KTH-RPL/Pluto-ATRV/images/gps.jpg

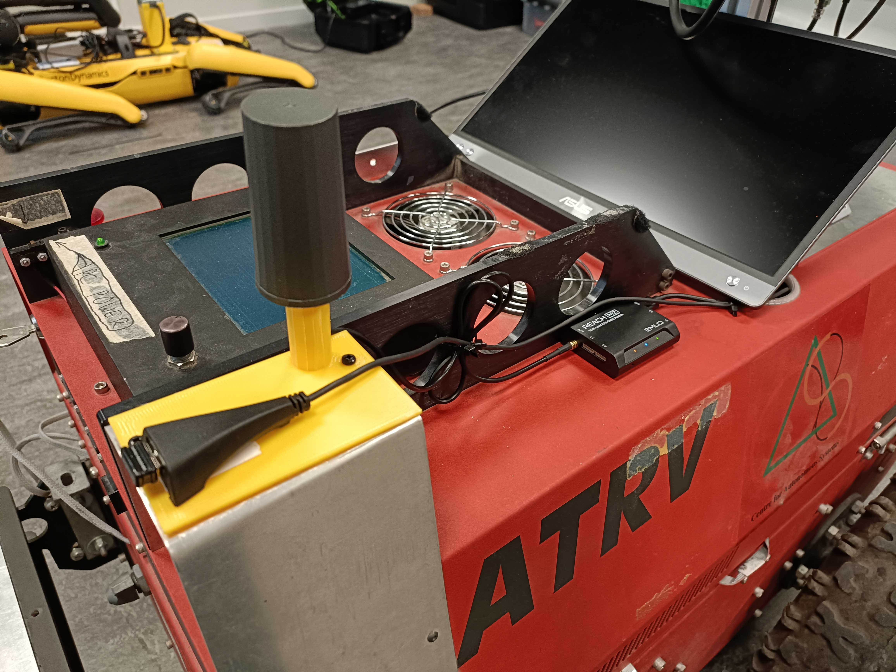
images/gps.jpg
